flyinggorilla/ultimaker-s5/formfutura spool adapter/20200627_124741780_iOS.jpg

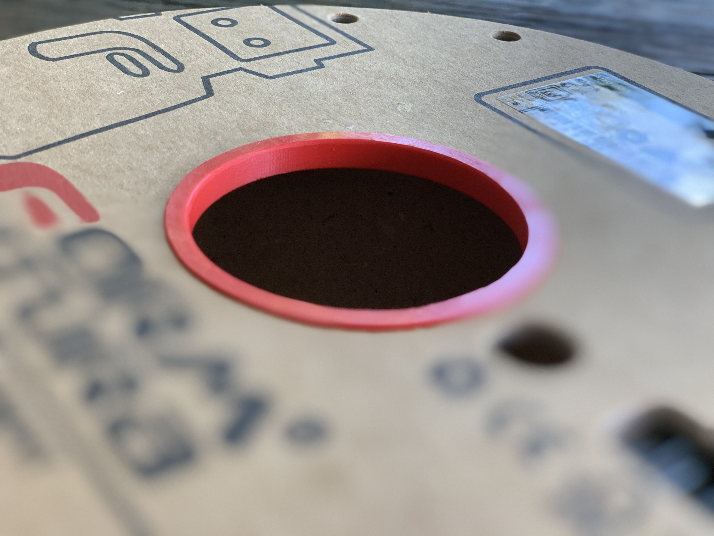
formfutura spool adapter/20200627_124741780_iOS.jpg
