flyinggorilla/ultimaker-s5/formfutura spool adapter/20200627_124826044_iOS.jpg

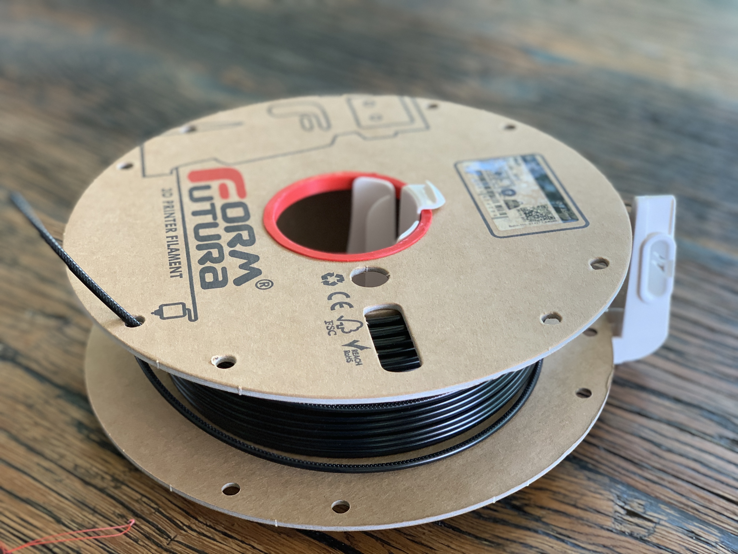
formfutura spool adapter/20200627_124826044_iOS.jpg
