flyinggorilla/ultimaker-s5/formfutura spool adapter/20200628_083236085_iOS.jpg

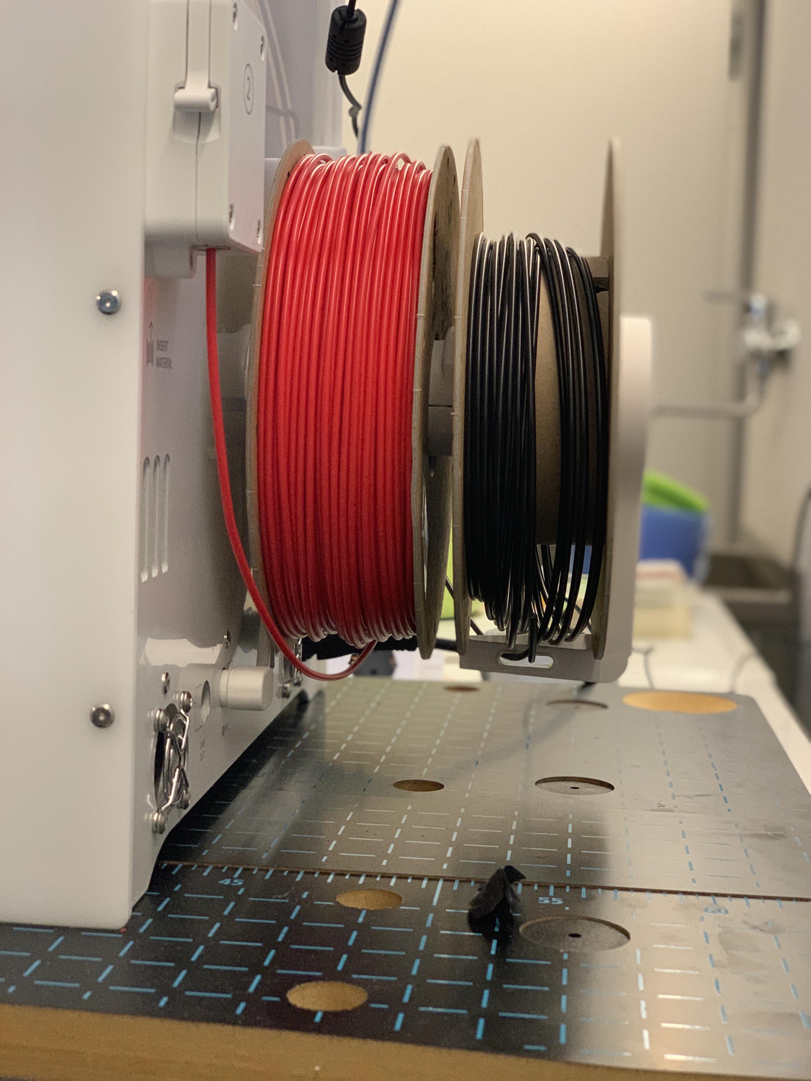
formfutura spool adapter/20200628_083236085_iOS.jpg
