flyinggorilla/ultimaker-s5/formfutura spool adapter/20200628_083302297_iOS.jpg

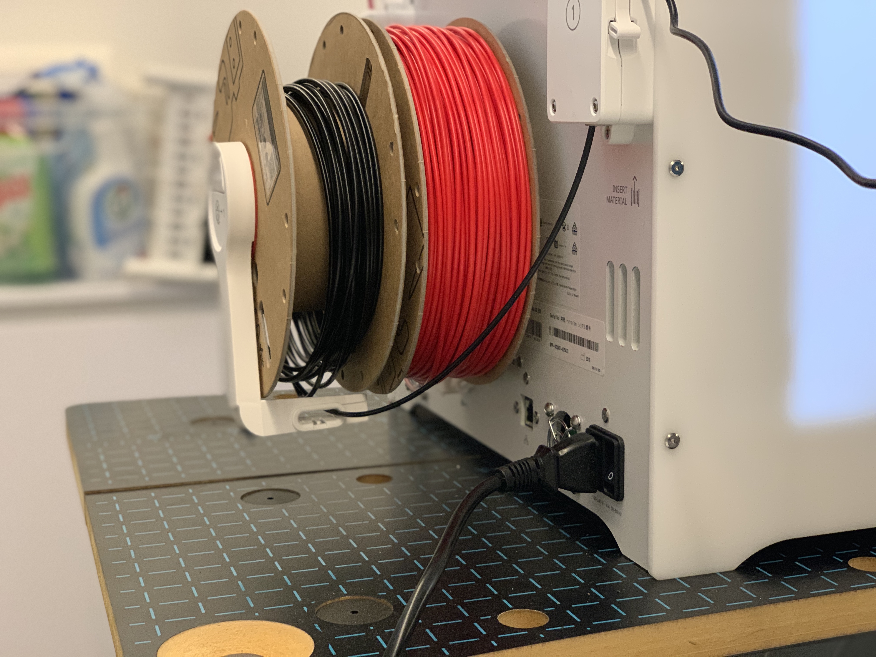
formfutura spool adapter/20200628_083302297_iOS.jpg
